luicer/AxxSolder/Other/SerialPlot_settings.ini

[MainWindow]
size=@Size(2560 1377)
pos=@Point(-1 -8)
activePanel=DataFormat
hidePanels=false
maximized=true
state=@ByteArray(\0\0\0\xff\0\0\0\0\xfd\0\0\0\0\0\0\n\0\0\0\x5\x16\0\0\0\x4\0\0\0\x4\0\0\0\b\0\0\0\b\xfc\0\0\0\x1\0\0\0\x2\0\0\0\x3\0\0\0\f\0t\0\x62\0P\0l\0o\0t\x1\0\0\0\0\xff\xff\xff\xff\0\0\0\0\0\0\0\0\0\0\0\x1a\0t\0\x62\0P\0o\0r\0t\0\x43\0o\0n\0t\0r\0o\0l\x1\0\0\0i\xff\xff\xff\xff\0\0\0\0\0\0\0\0\0\0\0\x10\0t\0\x62\0R\0\x65\0\x63\0o\0r\0\x64\x1\0\0\x2\x5\xff\xff\xff\xff\0\0\0\0\0\0\0\0)

[Port]
selectedPort=COM4
baudRate=256000
parity=none
dataBits=8
stopBits=1
flowControl=none

[DataFormat]
format=custom

[DataFormat_Binary]
numOfChannels=2
numberFormat=float
endianness=little

[DataFormat_ASCII]
numOfChannels=9
delimiter=TAB
customDelimiter=|
filterMode=disabled
filterPrefix=

[DataFormat_CustomFrame]
numOfChannels=9
numberFormat=float
endianness=little
frameStart=AA
fixedSize=false
frameSize=36
checksum=false
debugMode=false

[Channels]
channel\1\name=ACTUAL TEMPERATURE
channel\1\color=@Variant(\0\0\0\x43\x1\xff\xff\xff\xff\0\0VV\0\0)
channel\1\visible=true
channel\1\gain=1
channel\1\gainEnabled=false
channel\1\offset=0
channel\1\offsetEnabled=false
channel\2\name=ACTUAL TEMPERATURE - Filtered
channel\2\color=@Variant(\0\0\0\x43\x1\xff\xff\xbc\xbc\0\0\0\0\0\0)
channel\2\visible=true
channel\2\gain=1
channel\2\gainEnabled=false
channel\2\offset=0
channel\2\offsetEnabled=false
channel\3\name=SetPoint
channel\3\color=@Variant(\0\0\0\x43\x1\xff\xff\xff\xff\0\0\xff\xff\0\0)
channel\3\visible=true
channel\3\gain=1
channel\3\gainEnabled=false
channel\3\offset=0
channel\3\offsetEnabled=false
channel\4\name=Power
channel\4\color=@Variant(\0\0\0\x43\x1\xff\xffUU\xff\xff\0\0\0\0)
channel\4\visible=true
channel\4\gain=1
channel\4\gainEnabled=false
channel\4\offset=0
channel\4\offsetEnabled=false
channel\5\name=Power - Filtered
channel\5\color="@Variant(\0\0\0\x43\x1\xff\xff;;\xb0\xb0VV\0\0)"
channel\5\visible=true
channel\5\gain=1
channel\5\gainEnabled=false
channel\5\offset=0
channel\5\offsetEnabled=false
channel\6\name=P-PART
channel\6\color=@Variant(\0\0\0\x43\x1\xff\xff\0\0\0\0\xff\xff\0\0)
channel\6\visible=true
channel\6\gain=1
channel\6\gainEnabled=false
channel\6\offset=0
channel\6\offsetEnabled=false
channel\7\name=I-PART
channel\7\color=@Variant(\0\0\0\x43\x1\xff\xff\xff\xff\xaa\xaa\0\0\0\0)
channel\7\visible=true
channel\7\gain=1
channel\7\gainEnabled=false
channel\7\offset=0
channel\7\offsetEnabled=false
channel\8\name=D-PART
channel\8\color=@Variant(\0\0\0\x43\x1\xff\xff\0\0\0\0\0\0\0\0)
channel\8\visible=true
channel\8\gain=1
channel\8\gainEnabled=false
channel\8\offset=0
channel\8\offsetEnabled=false
channel\size=10
channel\9\name=Measured Current
channel\9\color=@Variant(\0\0\0\x43\x1\xff\xff\xb4\xb4\xb4\xb4\0\0\0\0)
channel\9\visible=true
channel\9\gain=1
channel\9\gainEnabled=false
channel\9\offset=0
channel\9\offsetEnabled=false
channel\10\name=Channel 10
channel\10\color=@Variant(\0\0\0\x43\x1\xff\xff\x85\x85\xa9\xa9\0\0\0\0)
channel\10\visible=true
channel\10\gain=1
channel\10\gainEnabled=false
channel\10\offset=0
channel\10\offsetEnabled=false

[Plot]
numOfSamples=1000
plotWidth=1000
indexAsX=true
xMax=1000
xMin=0
autoScale=false
yMax=400
yMin=-100
darkBackground=false
grid=false
minorGrid=false
legend=true
multiPlot=false
symbols=auto
numLines=1000
decimals=6

[Commands]
command\1\name=Command 1
command\1\type=ascii
command\1\data=
command\size=1

[Record]
autoIncrement=true
recordPaused=true
stopOnClose=true
header=true
disableBuffering=false
separator=","
decimals=6
timestamp=false
timestampFormat=seconds

[UpdateCheck]
periodicCheck=true
lastCheck=2025-01-02
