luicer/AxxSolder/AxxSolder_firmware/Core/Src/buzzer.c

#include "buzzer.h"

extern TIM_HandleTypeDef htim4;
extern TIM_HandleTypeDef htim17;

/* Beep the beeper */
void beep(float buzzer_enabled){
	if(buzzer_enabled == 1){
		HAL_TIM_PWM_Start_IT(&htim4, TIM_CHANNEL_2);
		HAL_TIM_Base_Start_IT(&htim17);
	}
}

/* Beep the beeper twice*/
void beep_startup(float buzzer_enabled){
	beep(buzzer_enabled);
	HAL_Delay(100);
	beep(buzzer_enabled);
}
